s-t-e-f-a-n/twinusb/assets/twinusb_20.png

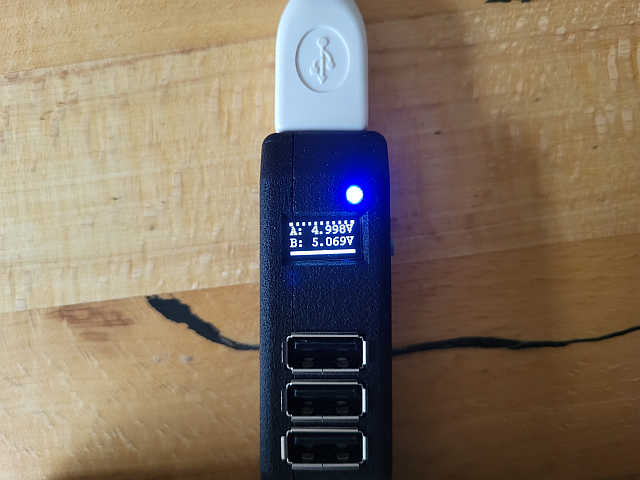
assets/twinusb_20.png
